impatrq/horus/horus_documentacion/Tabla costos.pdf

Componente | Cantidad | Precio Individual | Precio Parcial | Precio individual USD | Precio Parcial USD
Rasberry P9 4 Modelo B | 1 | $105.701,36 | $ 105.701,36 | $ 104,87 | $ 104,87
Raspberry Pi Pico | 2 | $12.279,000 | $ 24.558,00 | $ 12,17 | $ 24,33
Almacenamiento Externo Kingston | 1 | $12.698,00 | $ 12.698,00 | $ 12,58 | $ 12,58
Modulo Lora sx1278 | 2 | $17.487,00 | $ 34.974,00 | $ 17,35 | $ 34,70
Filamento Grilon3 PLA Gris | 3 | $14.987,00 | $ 44.961,00 | $ 14,87 | $ 44,61
Baterias de Gel 12v | 2 | $23.110,00 | $ 46.220,00 | $ 22,93 | $ 45,86
Camara Web Q Plus | 1 | $17.915,00 | $ 17.915,00 | $ 17,75 | $ 17,75
Módulo GPS | 1 | $12.638,00 | $ 12.638,00 | $ 12,54 | $ 12,54
Modulo A4988 (Drivers) | 2 | $2.079,00 | $ 4.158,00 | $ 2,06 | $ 4,12
PCB | 1 | $ 15.900,00 | $ 15.900,00 | $ 15,75 | $ 15,75
Plancha de aluminio 30x30 | 1 | $14.498,00 | $ 14.498,00 | $ 14,36 | $ 14,36
Cable dupont macho-hembra | 1 | $2.239,00 | $ 2.239,00 | $ 2,22 | $ 2,22
Cable dupont macho-macho | 1 | $2.229,00 | $ 2.229,00 | $ 2,21 | $ 2,21
Servo Digital Mg996 Mg996r | 2 | $12.100,00 | $ 24.200,00 | $ 12,00 | $ 24,00
Tira de Pines | 1 | $3.880,00 | $ 3.880,00 | $ 3,84 | $ 3,84
Servo Motor SG90 | 1 | $3.846,00 | $ 3.846,00 | $ 3,82 | $ 3,82
Total Pesos (Noviembre 2024): | $ 370.615,36 | Total USD: | $ 367,56
