impatrq/horus/Estructura_HORUS/peso_y_dimensiones.pdf

Pesos y tamaño
Estructura 400x400 peso 1kg motores 43x43x40 255g

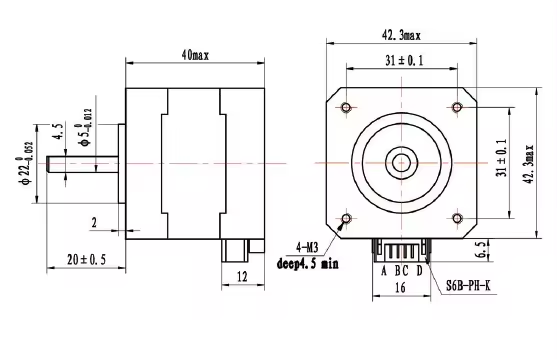
[picture p3: figure]

servo 40x20x44 peso 55g

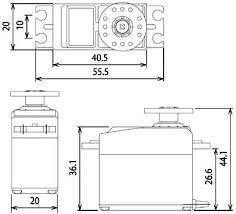
[picture p4: figure]

camara 36x36 peso 15g

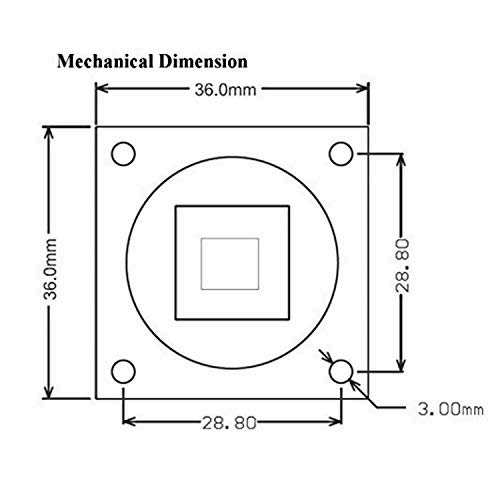
[picture p5: figure]

raspberry pi 4 88 x 58 x 18,5 peso 100g

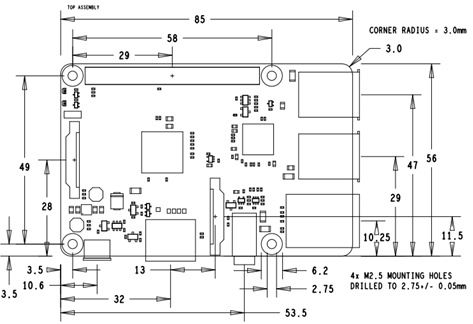
[picture p6: figure]

lectora de sd 45x21 peso 7.2g

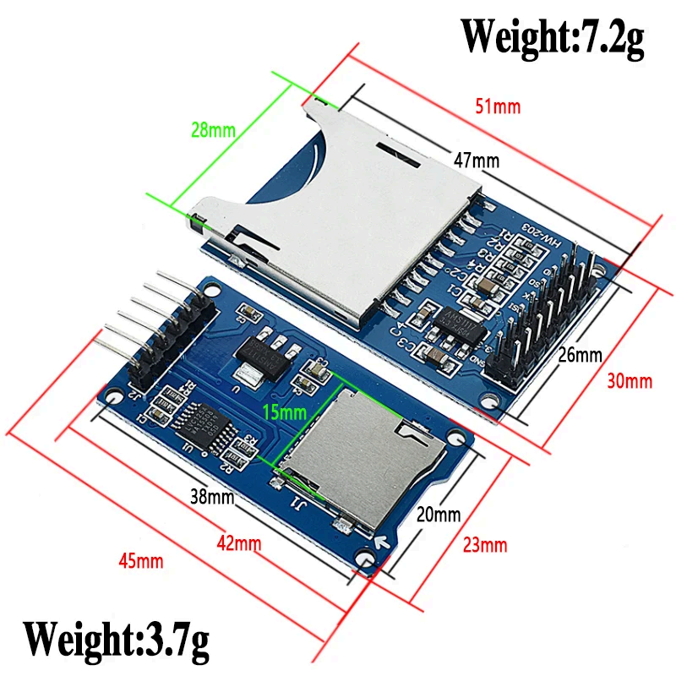
[picture p7: figure]

geolocalizador 35x25 peso 17g

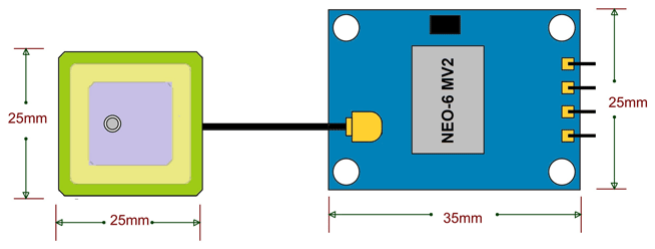
[picture p8: figure]

adaptador 16x15.2 peso 15g

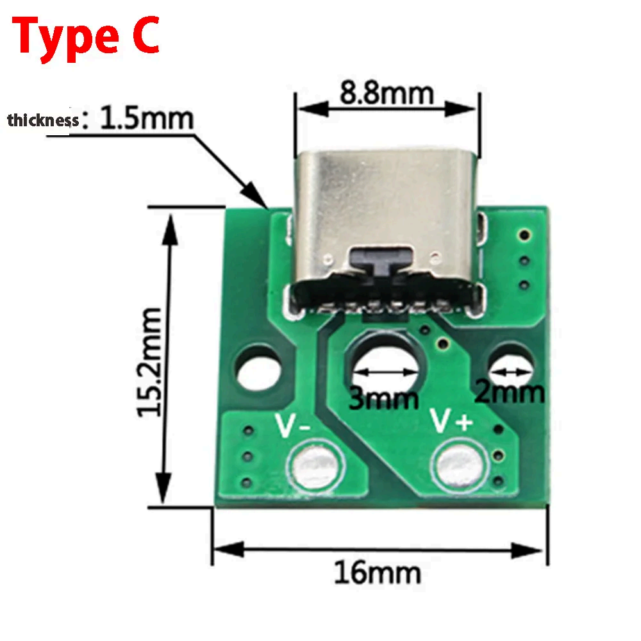
[picture p9: figure]

modulo rf 30x50 peso 20g

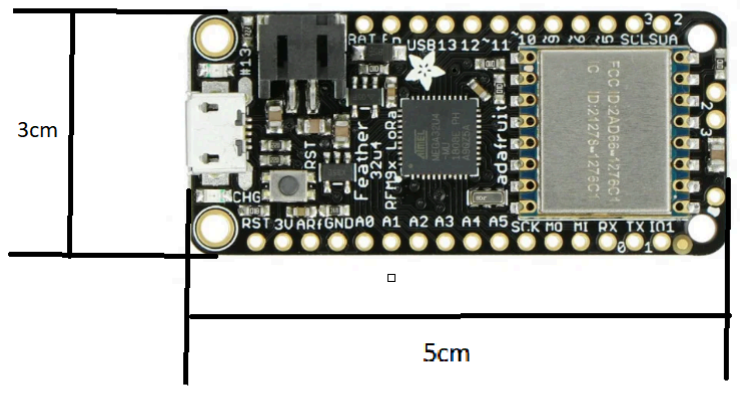
[picture p10: figure]

Bateria gel 12v 5ah 90x100x70

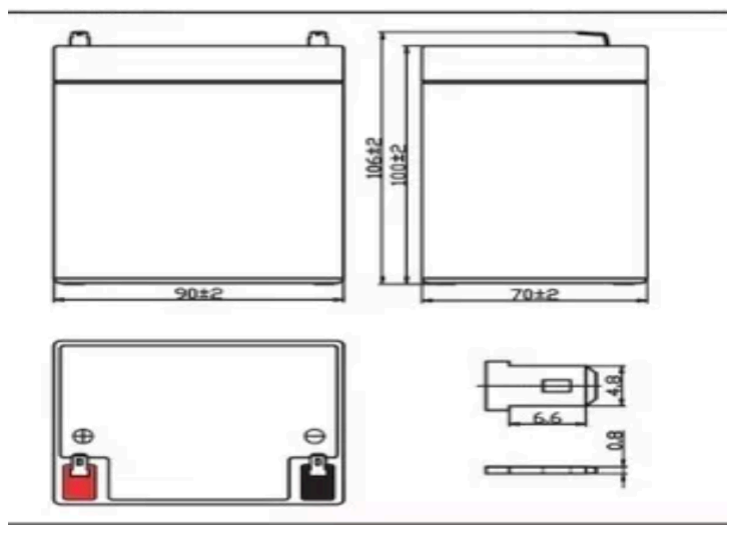
[picture p11: figure]
