impatrq/horus/Estructura_HORUS/Imagenes/adaptador eje elevador.png

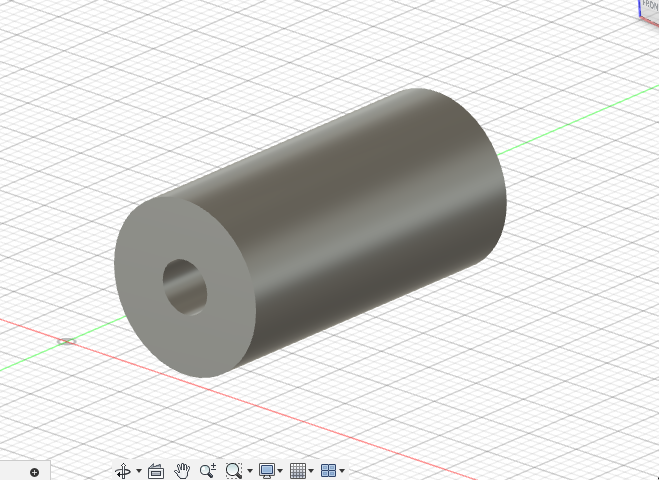
Estructura_HORUS/Imagenes/adaptador eje elevador.png
