impatrq/horus/Estructura_HORUS/Imagenes/agarre tuerca brazo elevador.png

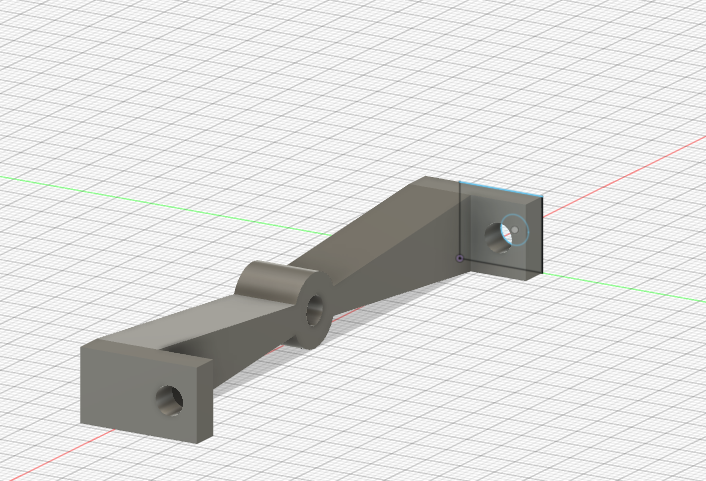
Estructura_HORUS/Imagenes/agarre tuerca brazo elevador.png
