impatrq/horus/Estructura_HORUS/Imagenes/base brazo.png

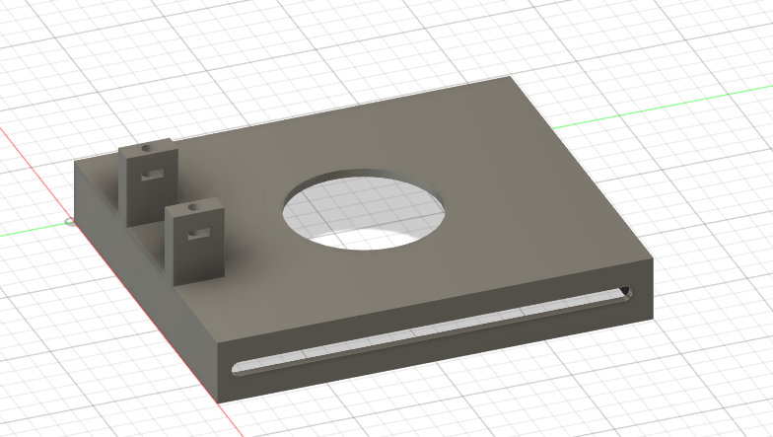
Estructura_HORUS/Imagenes/base brazo.png
