impatrq/horus/Estructura_HORUS/Imagenes/controladora sttepers.png

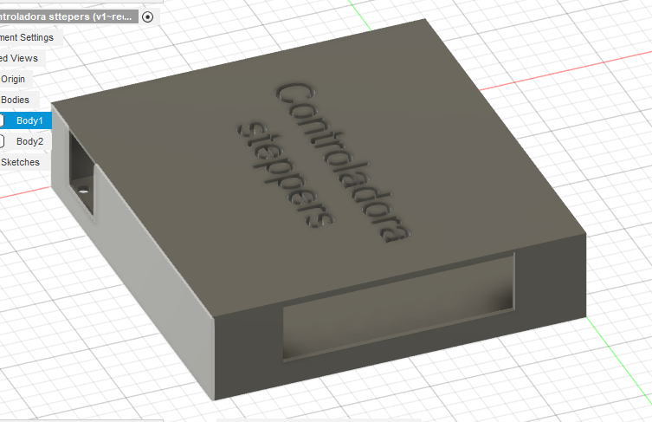
Estructura_HORUS/Imagenes/controladora sttepers.png
