impatrq/horus/Estructura_HORUS/Imagenes/refuerzo brazo.png

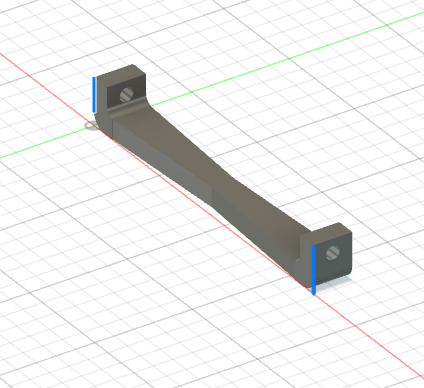
Estructura_HORUS/Imagenes/refuerzo brazo.png
