impatrq/horus/Estructura_HORUS/Imagenes/soporte bateria.png

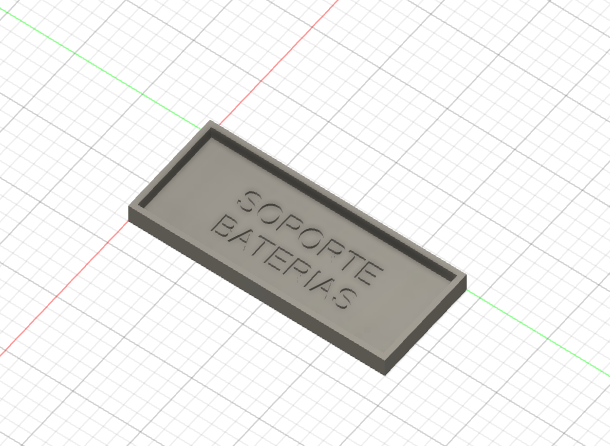
Estructura_HORUS/Imagenes/soporte bateria.png
