impatrq/horus/Estructura_HORUS/Imagenes/soporte camara.png

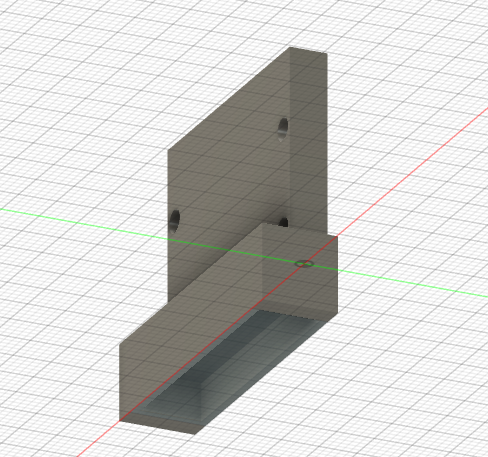
Estructura_HORUS/Imagenes/soporte camara.png
