impatrq/horus/Estructura_HORUS/Imagenes/soporte motor.png

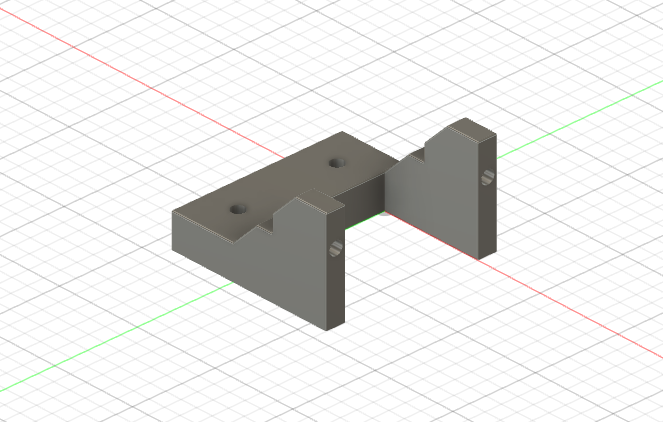
Estructura_HORUS/Imagenes/soporte motor.png
