impatrq/horus/Estructura_HORUS/Imagenes/suspension armada.png

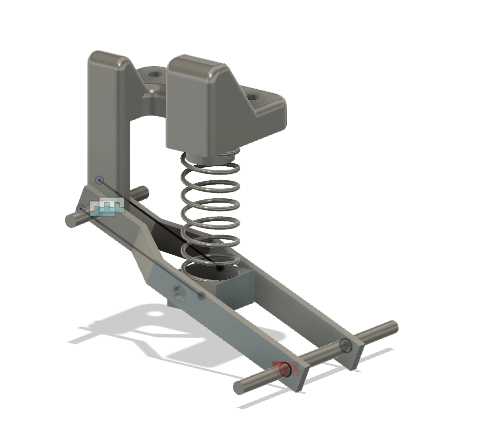
Estructura_HORUS/Imagenes/suspension armada.png
