impatrq/horus/Estructura_HORUS/Imagenes/tensor orugas.png

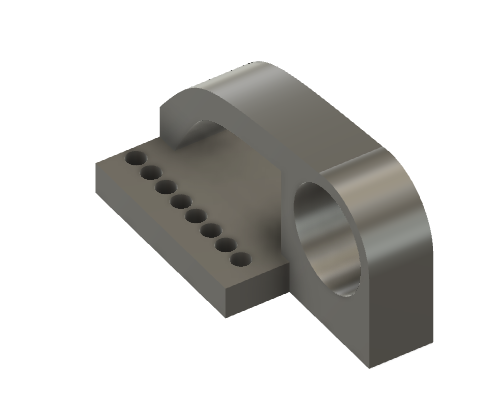
Estructura_HORUS/Imagenes/tensor orugas.png
