impatrq/horus/Estructura_HORUS/Primeros diseños/WhatsApp Image 2024-10-21 at 4.15.37 PM (1).jpeg

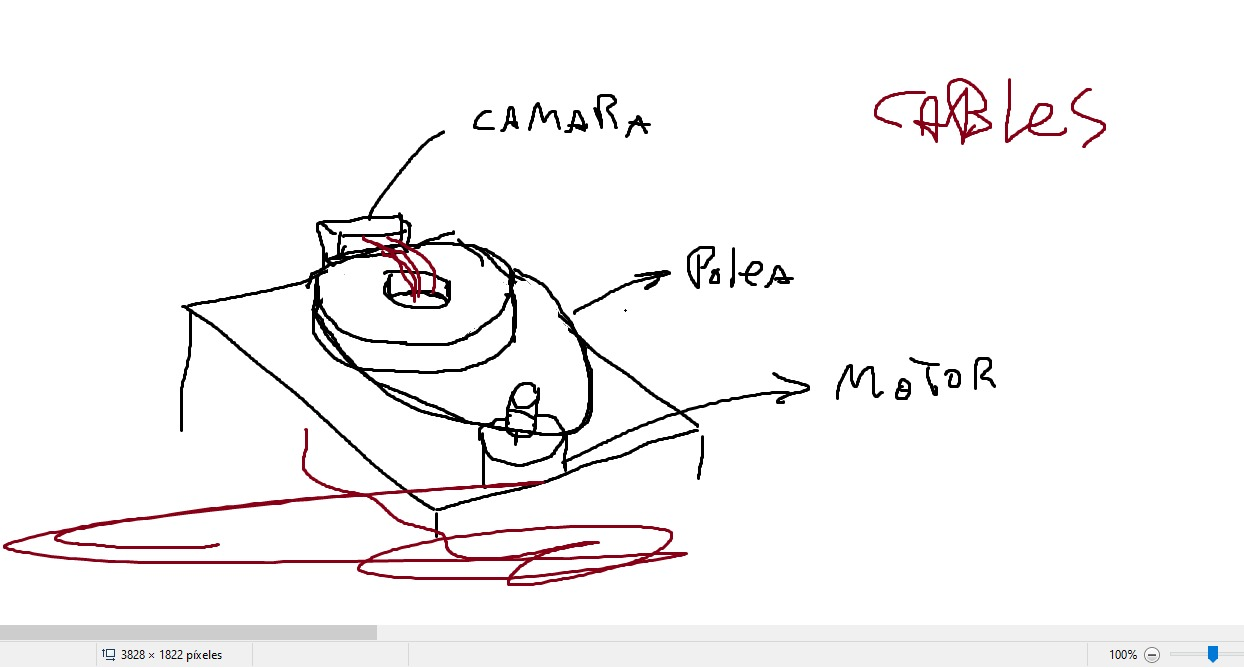
Estructura_HORUS/Primeros diseños/WhatsApp Image 2024-10-21 at 4.15.37 PM (1).jpeg
