impatrq/horus/horus_app/frontend/src/assets/boton-menos.png

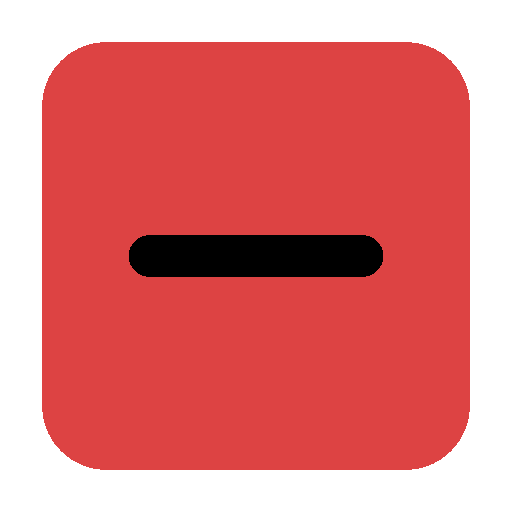
horus_app/frontend/src/assets/boton-menos.png
