impatrq/horus/horus_app/frontend/src/assets/delete.png

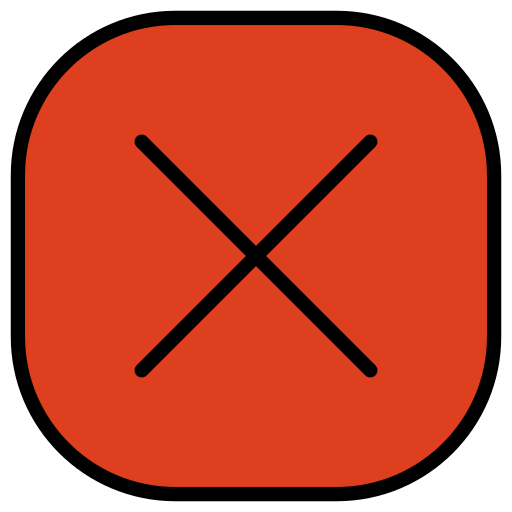
horus_app/frontend/src/assets/delete.png
