impatrq/horus/horus_app/frontend/src/assets/error.png

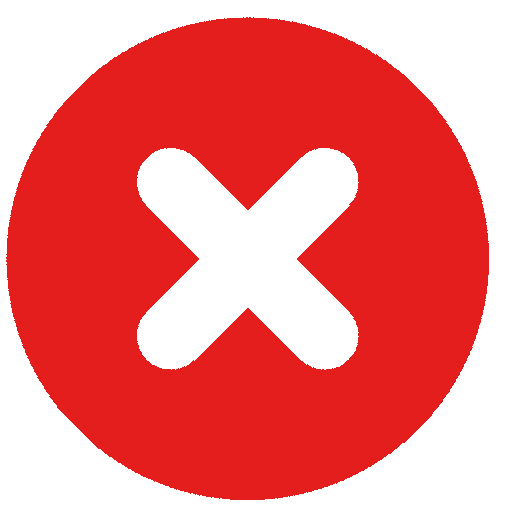
horus_app/frontend/src/assets/error.png
