impatrq/horus/horus_app/frontend/src/assets/mapas-y-banderas (1).png

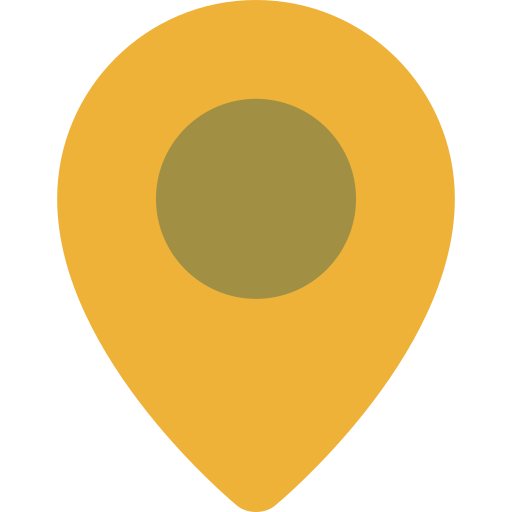
horus_app/frontend/src/assets/mapas-y-banderas (1).png
