impatrq/horus/horus_app/frontend/src/assets/mapas-y-banderas (2).png

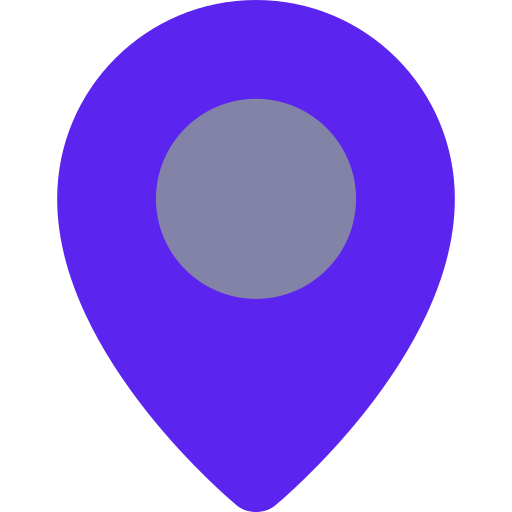
horus_app/frontend/src/assets/mapas-y-banderas (2).png
