impatrq/horus/horus_app/frontend/src/assets/Ojo de Horus.png

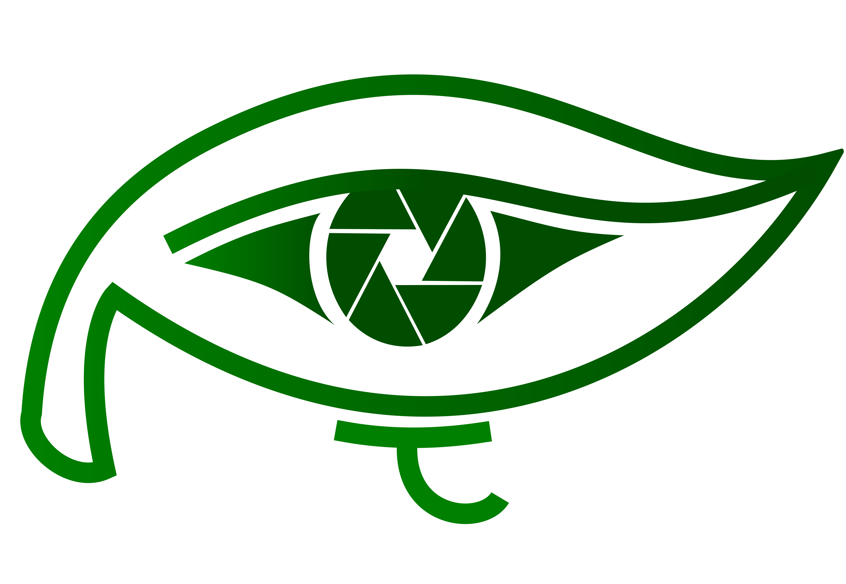
horus_app/frontend/src/assets/Ojo de Horus.png
