impatrq/horus/horus_documentacion/HORUS.jpg.jpeg

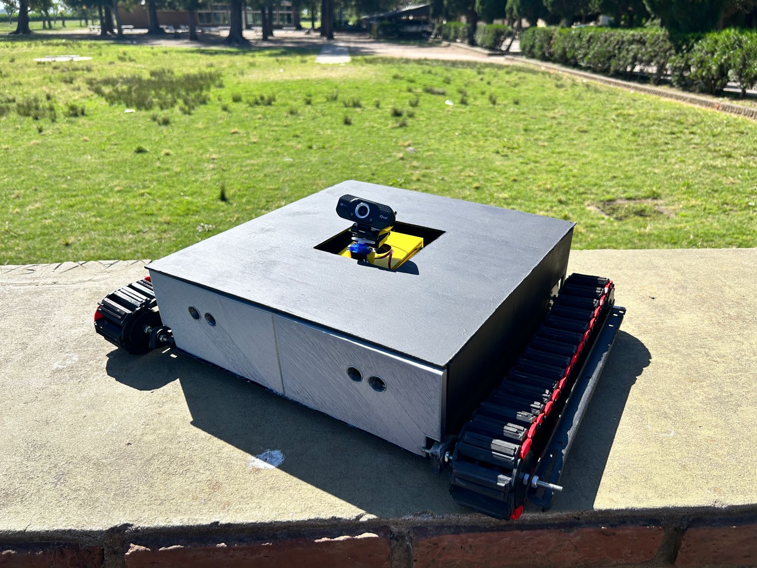
horus_documentacion/HORUS.jpg.jpeg
