impatrq/horus/horus_documentacion/Minimum valiable product.png

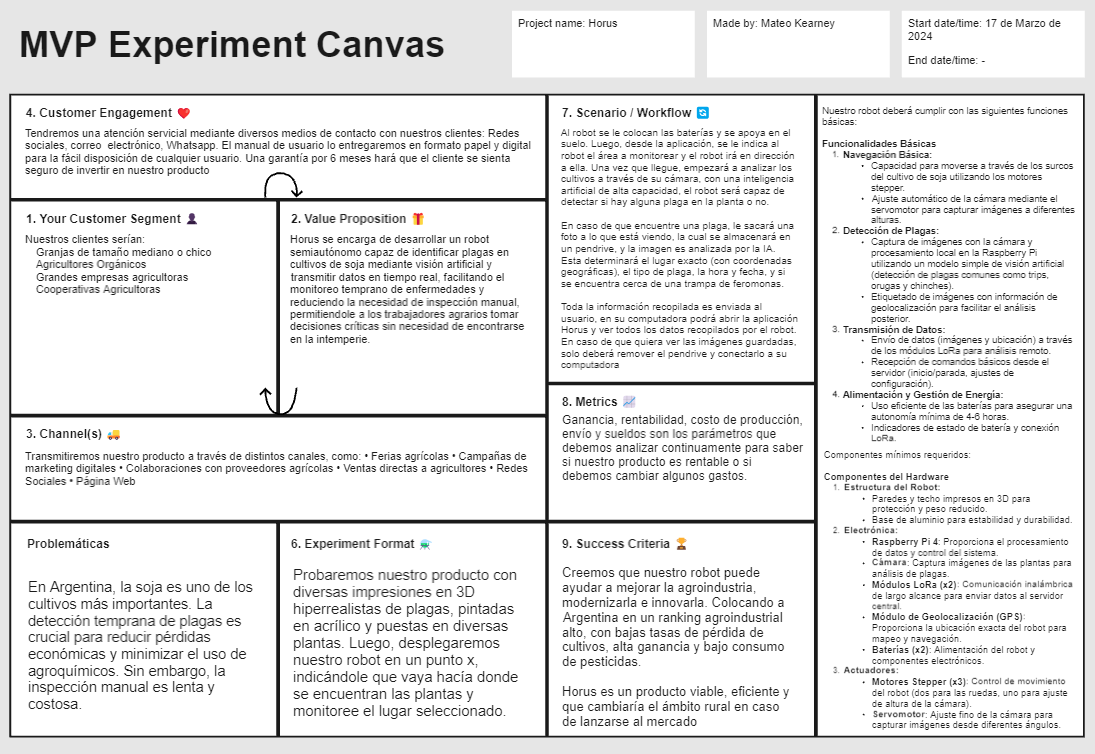
horus_documentacion/Minimum valiable product.png
