impatrq/horus/horus_electronics/Archivos Kicad pcb/NewEra.png

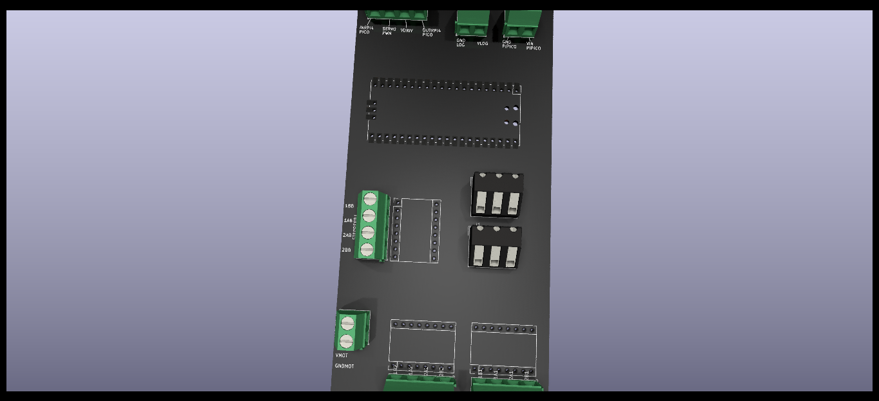
horus_electronics/Archivos Kicad pcb/NewEra.png
