impatrq/horus/horus_electronics/Archivos Kicad pcb/PCB STEPPER BRAZO/Screenshot_3.png

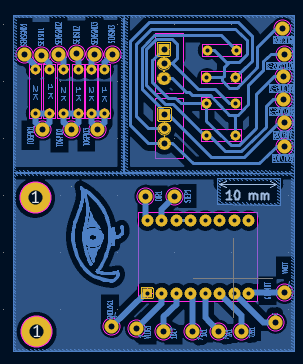
horus_electronics/Archivos Kicad pcb/PCB STEPPER BRAZO/Screenshot_3.png
