impatrq/horus/horus_electronics/misc Imagenes/3.png

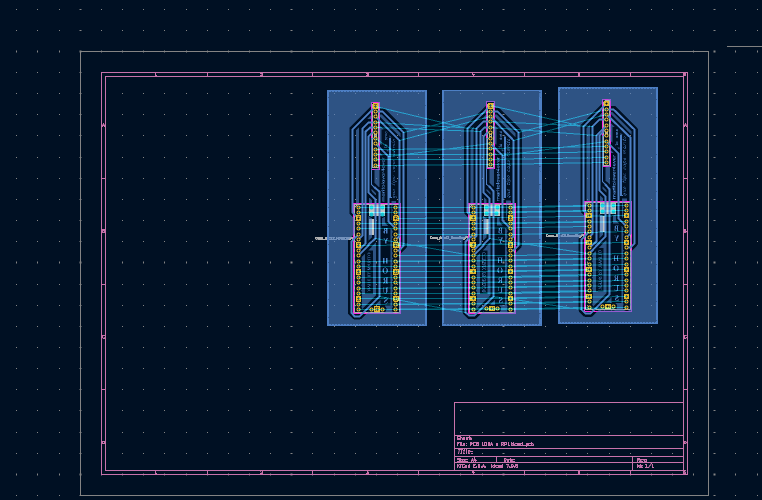
horus_electronics/misc Imagenes/3.png
