impatrq/horus/horus_electronics/misc Imagenes/A4988 conection diagram.png

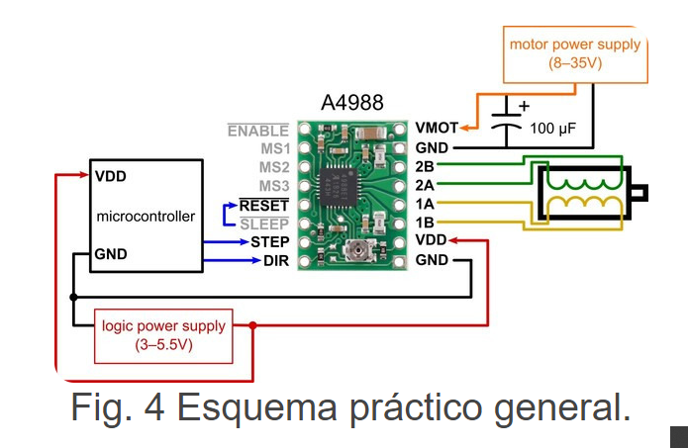
horus_electronics/misc Imagenes/A4988 conection diagram.png
