impatrq/horus/horus_electronics/misc Imagenes/NewEraVISUAL.png

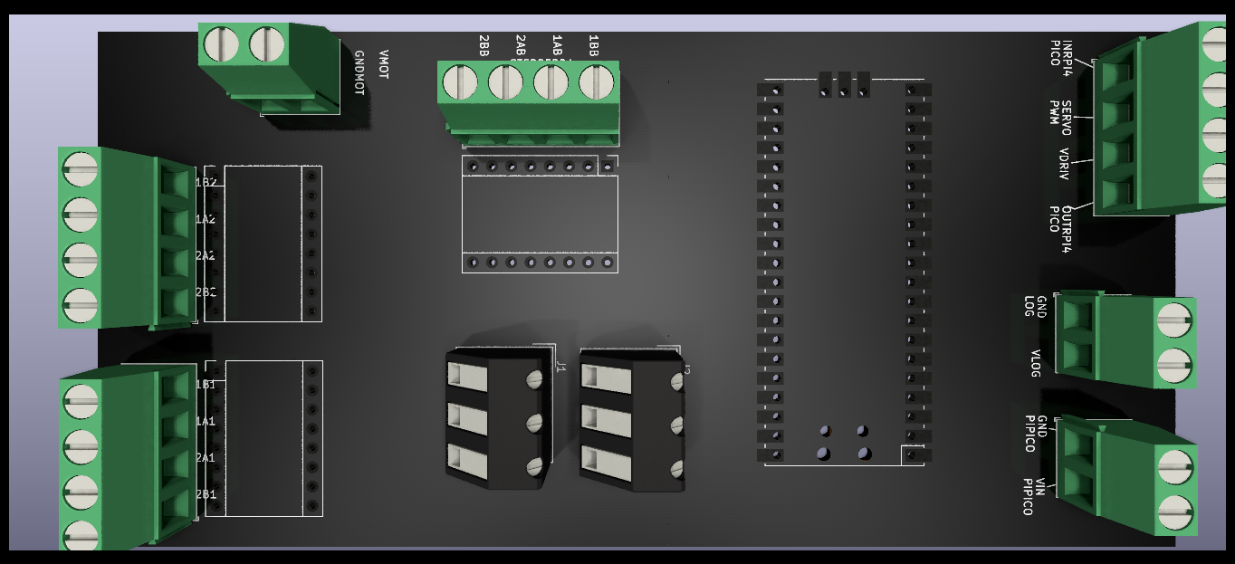
horus_electronics/misc Imagenes/NewEraVISUAL.png
