impatrq/horus/horus_electronics/misc Imagenes/pangeaPuenteh.jpg

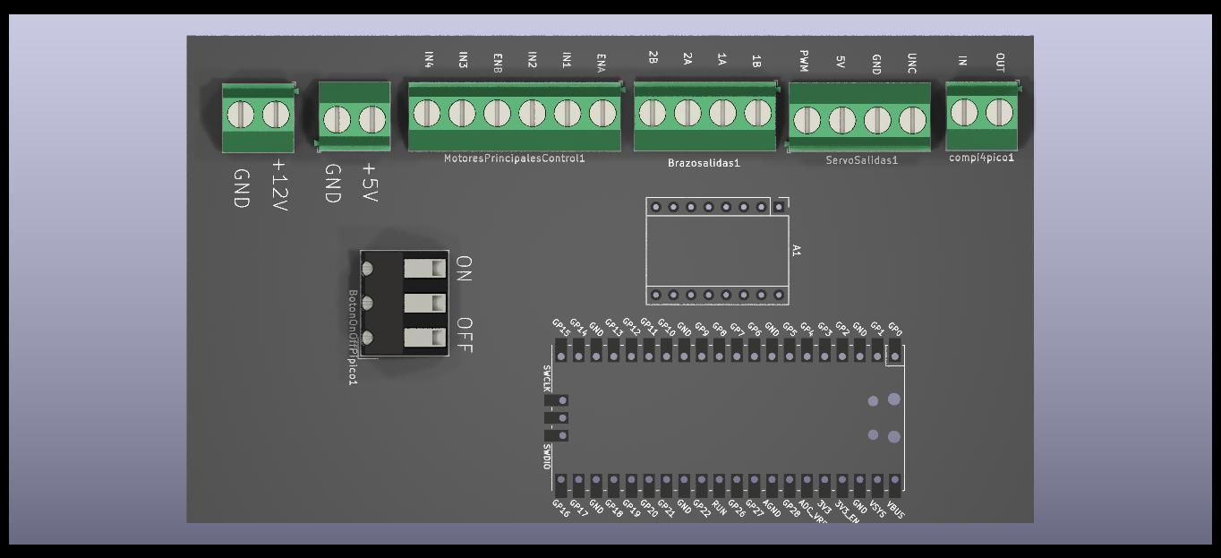
horus_electronics/misc Imagenes/pangeaPuenteh.jpg
