impatrq/horus/horus_electronics/misc Imagenes/pangeaPuenteh.jpg.png

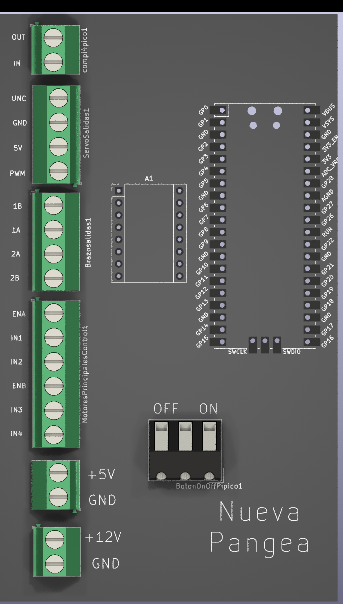
horus_electronics/misc Imagenes/pangeaPuenteh.jpg.png
