impatrq/horus/horus_electronics/misc Imagenes/Screenshot_1.png

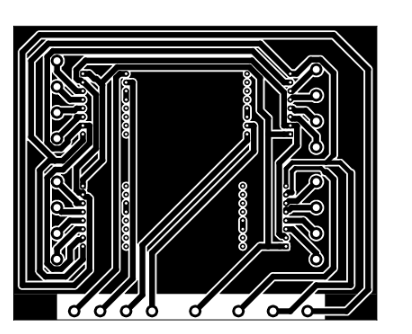
horus_electronics/misc Imagenes/Screenshot_1.png
