impatrq/horus/horus_electronics/misc Imagenes/Screenshot_3.png

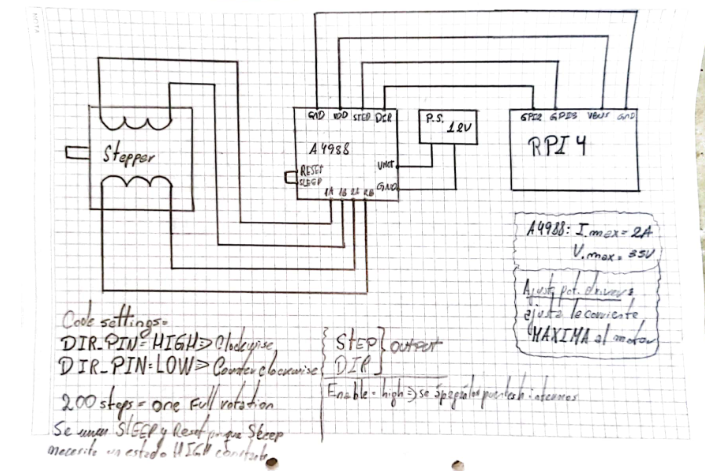
horus_electronics/misc Imagenes/Screenshot_3.png
