impatrq/horus/horus_electronics/misc Imagenes/Screenshot_4.png

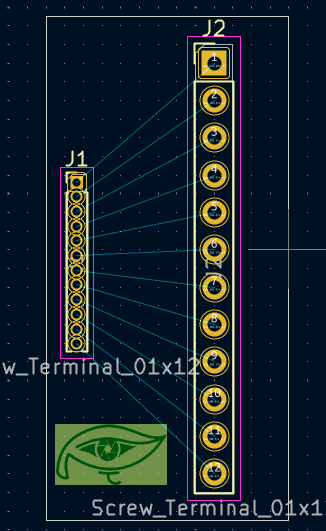
horus_electronics/misc Imagenes/Screenshot_4.png
