impatrq/horus/horus_electronics/misc Imagenes/Screenshot_5.png

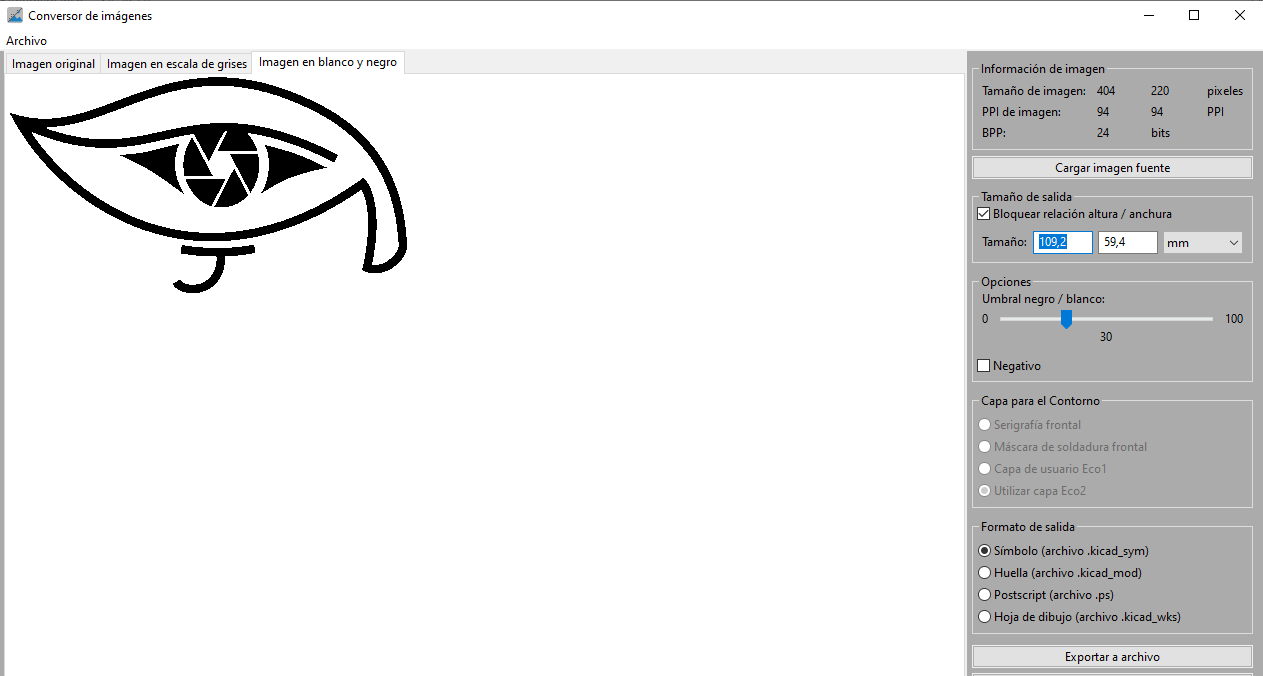
horus_electronics/misc Imagenes/Screenshot_5.png
