impatrq/horus/horus_electronics/misc Imagenes/Screenshot_6.png

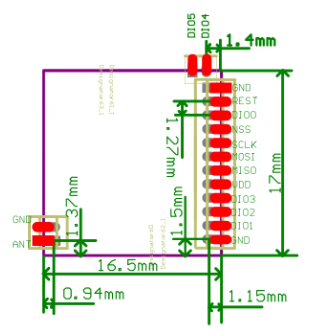
horus_electronics/misc Imagenes/Screenshot_6.png
