impatrq/horus/horus_paginaWeb/paginaWeb/dist/assets/Github-nDIyJ6BR.png

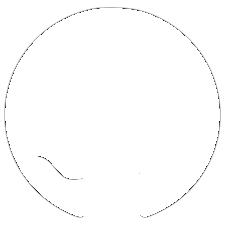
horus_paginaWeb/paginaWeb/dist/assets/Github-nDIyJ6BR.png
