impatrq/horus/horus_paginaWeb/paginaWeb/dist/assets/LinkedinBlanco-4YxeiaYb.png

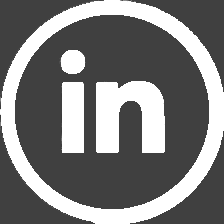
horus_paginaWeb/paginaWeb/dist/assets/LinkedinBlanco-4YxeiaYb.png
