impatrq/horus/horus_paginaWeb/paginaWeb/dist/assets/marito-BGvwKk_j.jpg

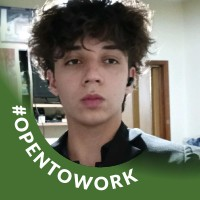
horus_paginaWeb/paginaWeb/dist/assets/marito-BGvwKk_j.jpg
