impatrq/horus/Estructura_HORUS/Archivos STL/estrcutura principal susp 1.stl

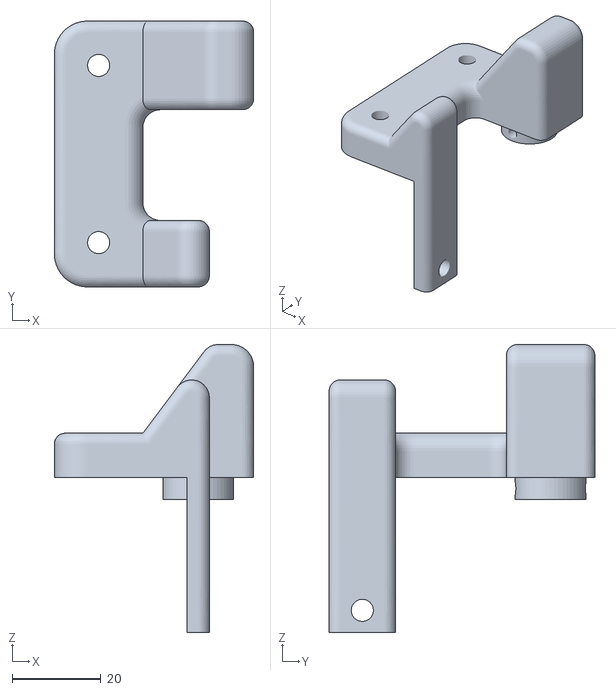
[picture p89: CAD file, 2024-11-26]
Estructura_HORUS/Archivos STL/estrcutura principal susp 1.stl
45.0 x 60.0 x 65.0
