impatrq/horus/Estructura_HORUS/Archivos STL/soporte baterias.stl

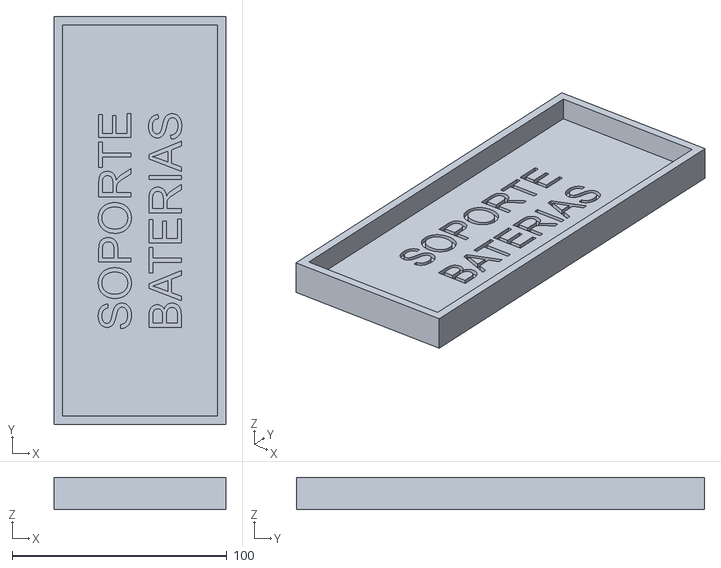
[picture p90: CAD file, 2024-11-26]
Estructura_HORUS/Archivos STL/soporte baterias.stl
80.0 x 190.0 x 15.0
