impatrq/horus/Estructura_HORUS/Archivos STL/soport servoo.stl

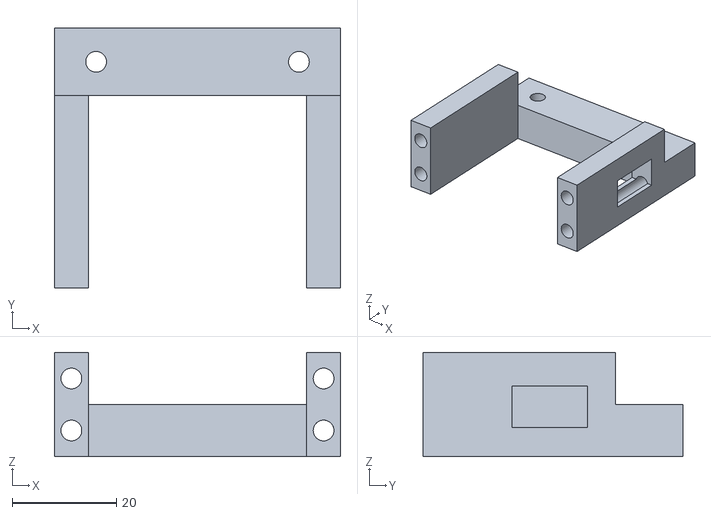
[picture p91: CAD file, 2024-11-26]
Estructura_HORUS/Archivos STL/soport servoo.stl
55.0 x 50.0 x 20.0
