impatrq/horus/Estructura_HORUS/Archivos STL/soporte motores.stl

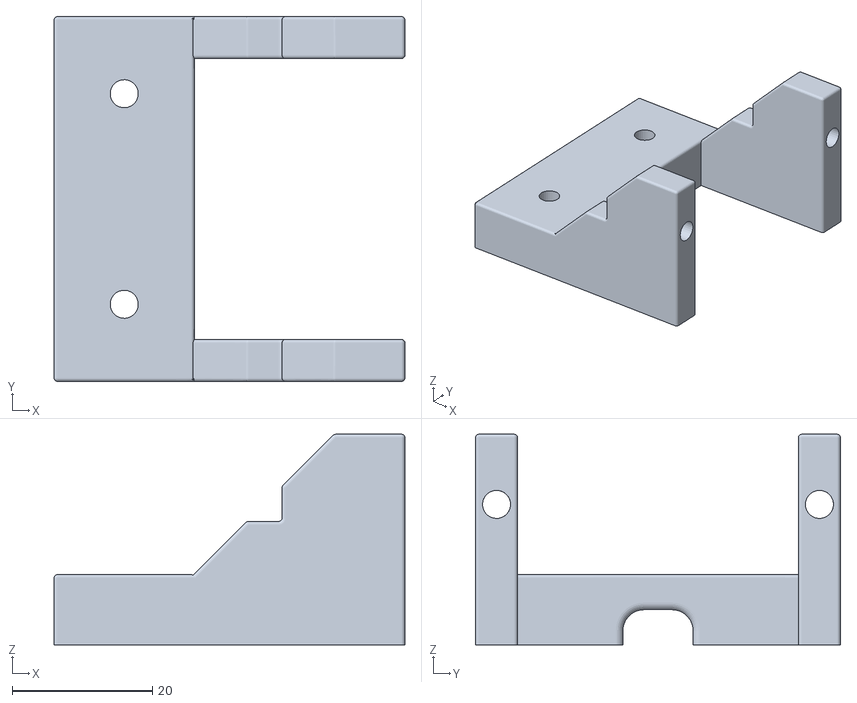
[picture p92: CAD file, 2024-11-26]
Estructura_HORUS/Archivos STL/soporte motores.stl
50.0 x 52.0 x 30.0
