impatrq/horus/Estructura_HORUS/Archivos STL/refuerzo brazo elevador.stl

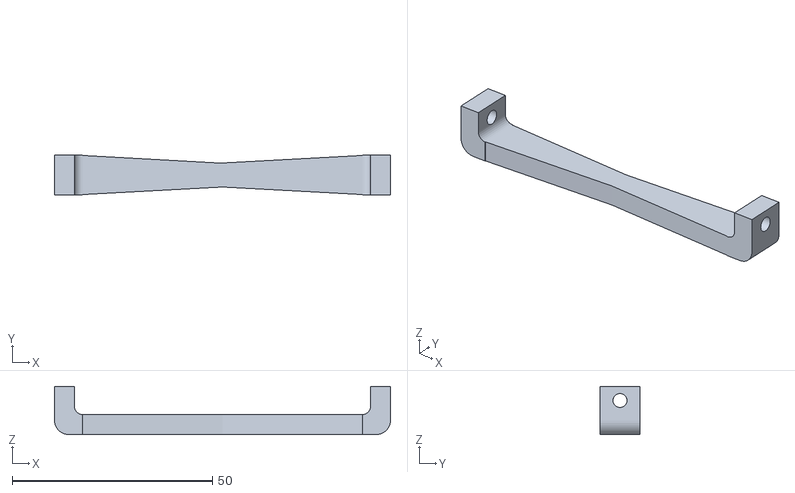
[picture p93: CAD file, 2024-11-26]
Estructura_HORUS/Archivos STL/refuerzo brazo elevador.stl
84.0 x 10.0 x 12.0
