impatrq/horus/Estructura_HORUS/Archivos STL/pasador orugas.stl

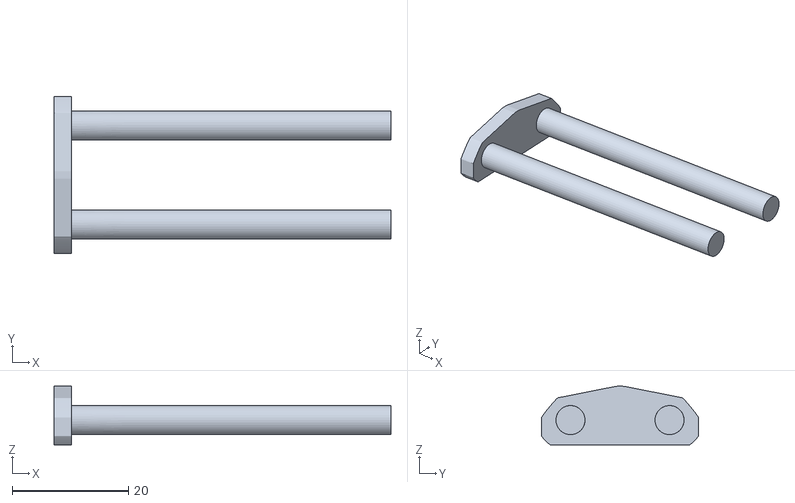
[picture p94: CAD file, 2024-11-26]
Estructura_HORUS/Archivos STL/pasador orugas.stl
58.0 x 27.0 x 10.1
