impatrq/horus/Estructura_HORUS/Archivos STL/tensor orgas .stl

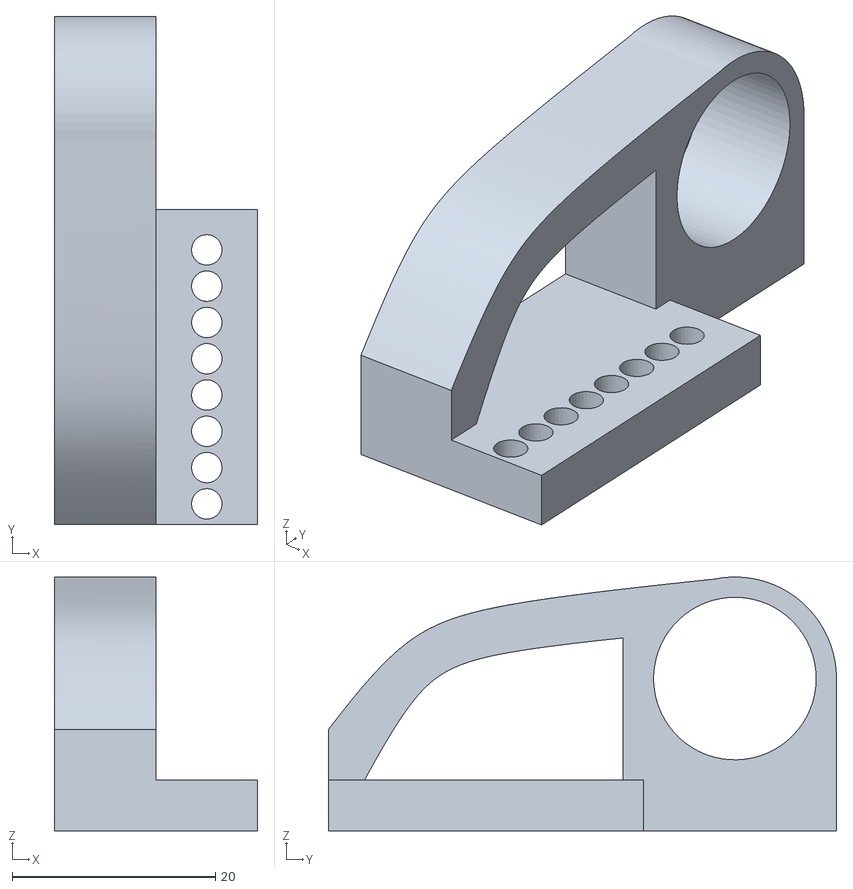
[picture p95: CAD file, 2024-11-26]
Estructura_HORUS/Archivos STL/tensor orgas .stl
20.0 x 50.0 x 25.0
