impatrq/horus/Estructura_HORUS/Archivos STL/rueda suspension .stl

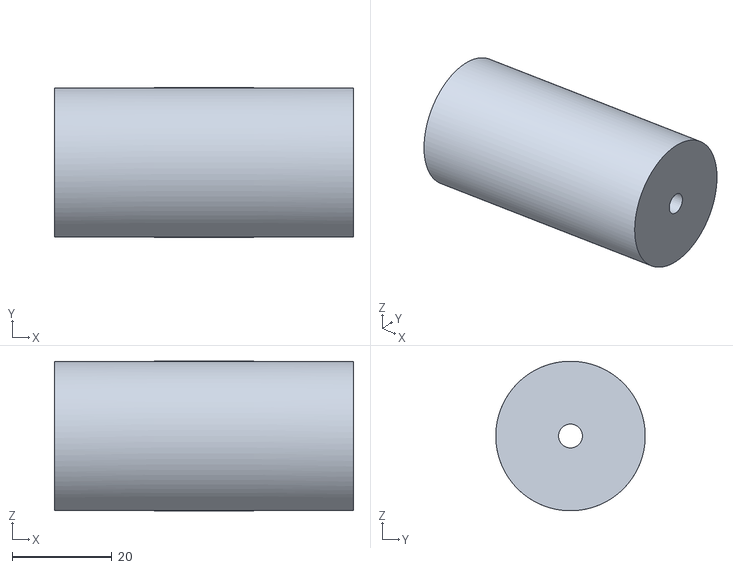
[picture p96: CAD file, 2024-11-26]
Estructura_HORUS/Archivos STL/rueda suspension .stl
60.0 x 30.0 x 30.0
