impatrq/horus/Estructura_HORUS/Archivos STL/soporte cam.stl

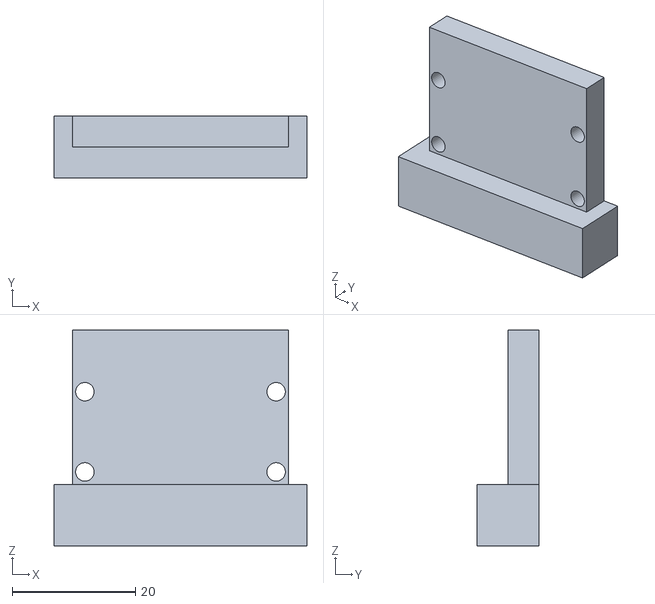
[picture p97: CAD file, 2024-11-26]
Estructura_HORUS/Archivos STL/soporte cam.stl
41.0 x 10.0 x 35.0
