impatrq/horus/Estructura_HORUS/Archivos STL/trabitas orugas.stl

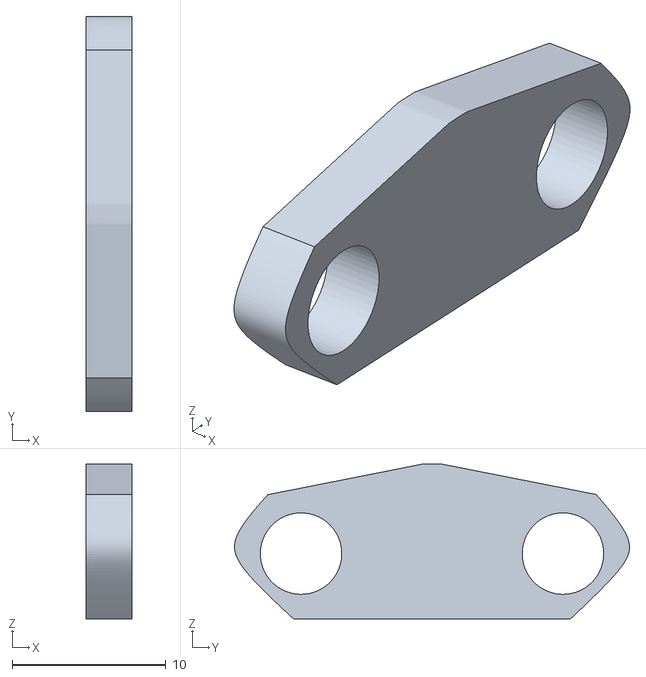
[picture p98: CAD file, 2024-11-26]
Estructura_HORUS/Archivos STL/trabitas orugas.stl
3.00 x 25.7 x 10.1
