impatrq/horus/Estructura_HORUS/Archivos STL/tapa controladora sttepers.stl

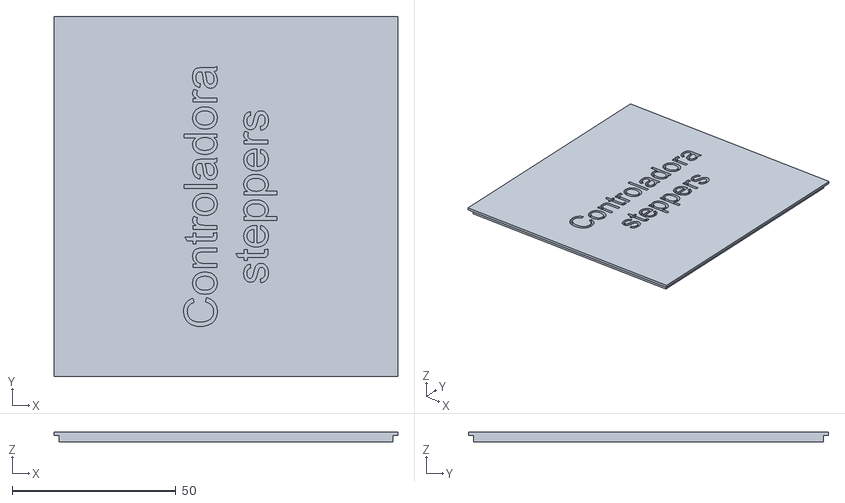
[picture p99: CAD file, 2024-11-26]
Estructura_HORUS/Archivos STL/tapa controladora sttepers.stl
105.0 x 110.0 x 3.00
