impatrq/horus/Estructura_HORUS/Archivos STL/agarre resorte.stl

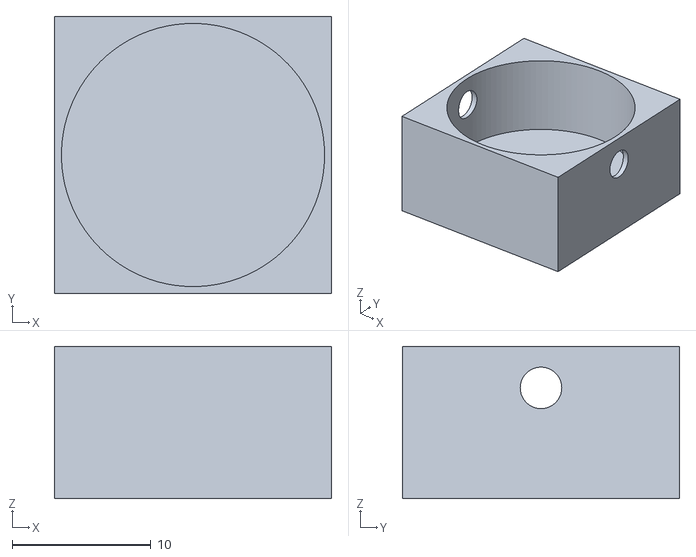
[picture p100: CAD file, 2024-11-26]
Estructura_HORUS/Archivos STL/agarre resorte.stl
20.0 x 20.0 x 11.0
