impatrq/horus/Estructura_HORUS/Archivos STL/base brazo elevador.stl

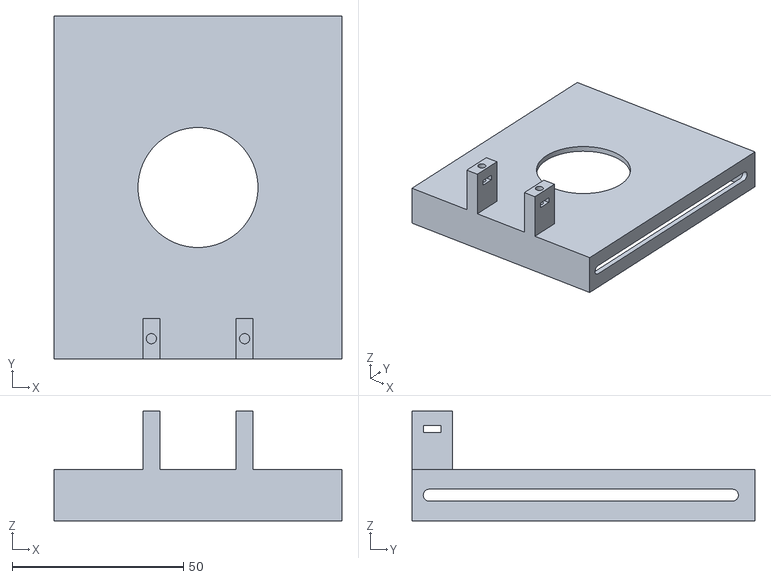
[picture p101: CAD file, 2024-11-26]
Estructura_HORUS/Archivos STL/base brazo elevador.stl
84.0 x 100.0 x 32.0
