impatrq/horus/Estructura_HORUS/Imagenes/brazo armado.png

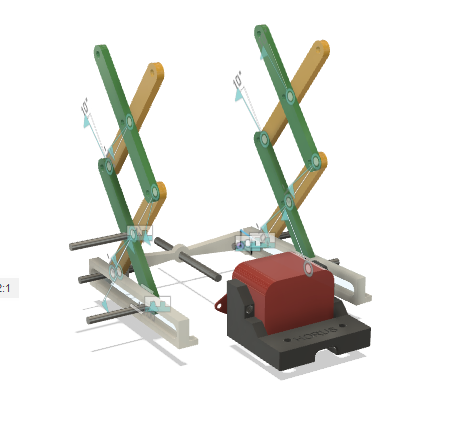
Estructura_HORUS/Imagenes/brazo armado.png
