impatrq/horus/horus_electronics/PDFS IMPRIMIBLES/PCB LORA TO RPI PICO.pdf

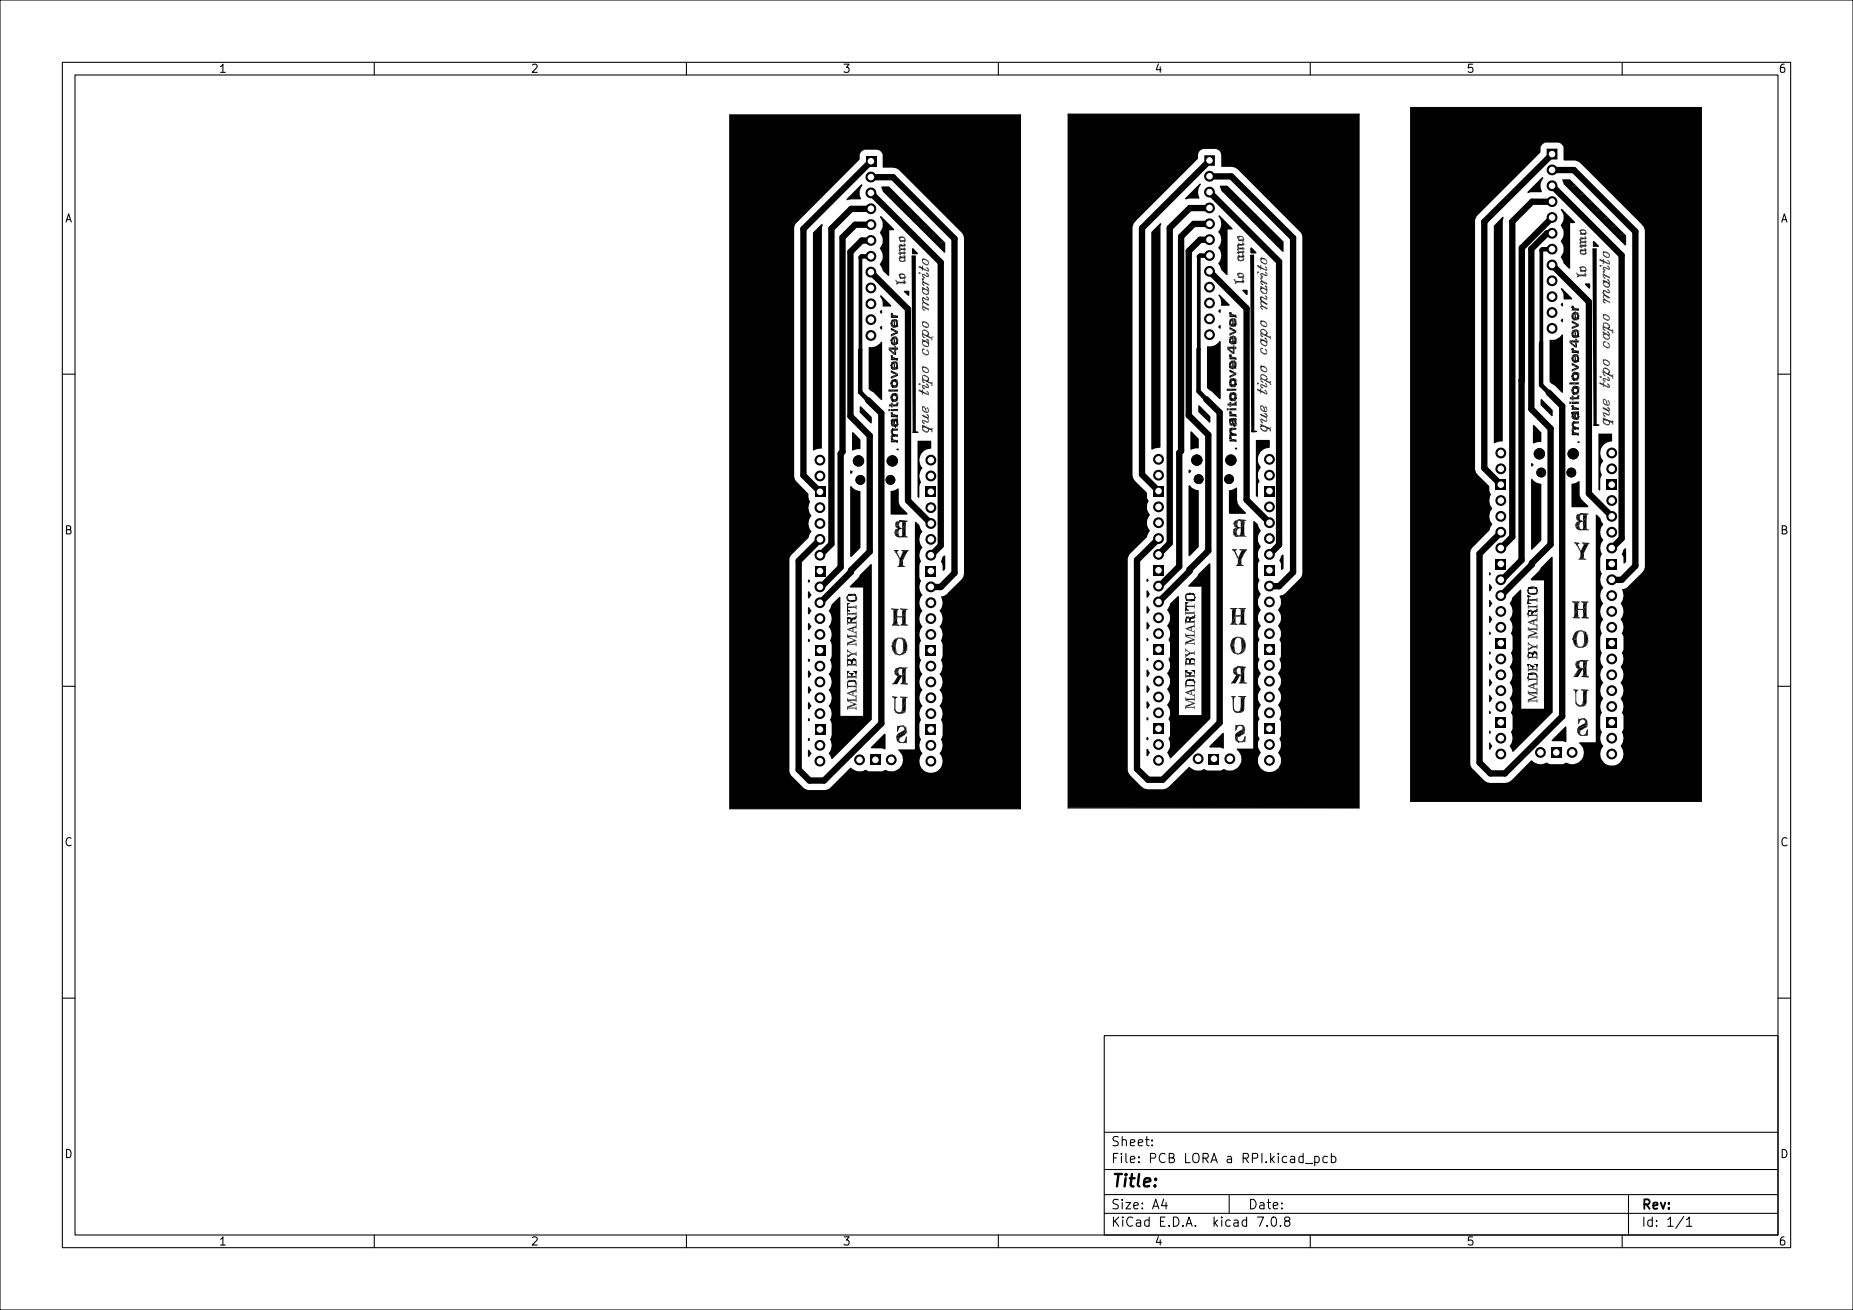
[picture p120: page 1]
