impatrq/horus/horus_documentacion/Medalla - Feed de Instagram.pdf

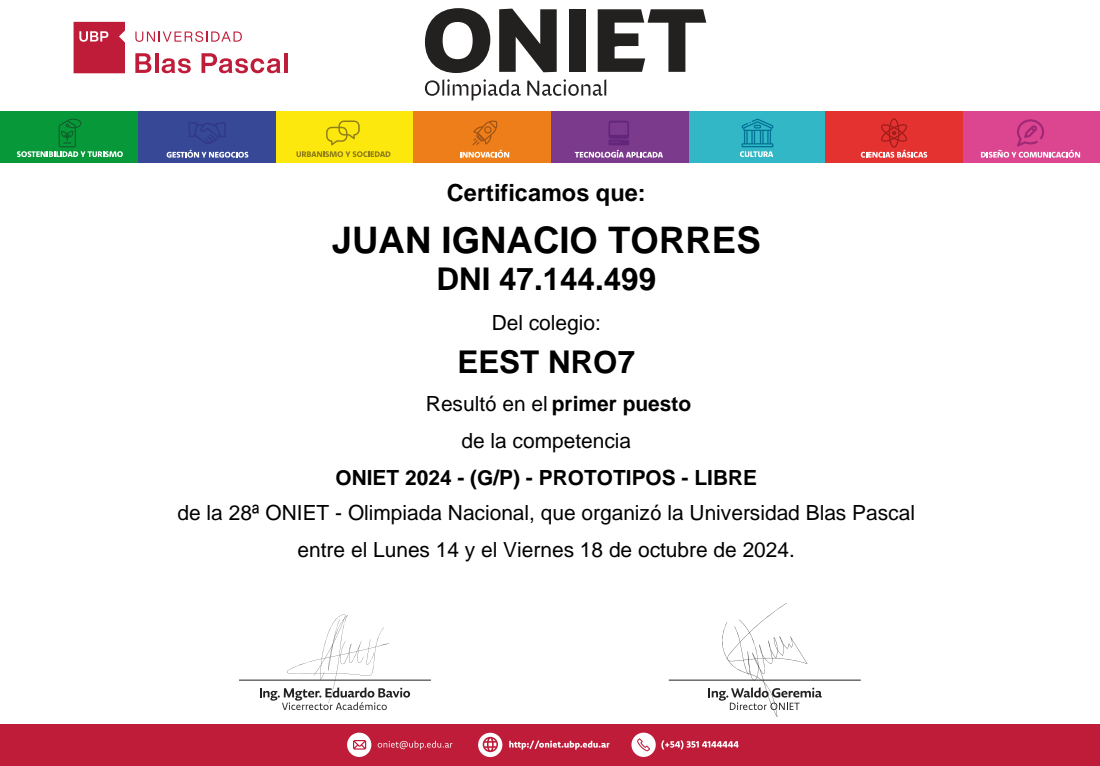
[picture p121: page 1]
Del colegio: EEST NRO7

Certificamos que:
JUAN IGNACIO TORRES
DNI 47.144.499

Resultó en el primer puesto
de la competencia

ONIET 2024 - (G/P) - PROTOTIPOS - LIBRE

de la 28ª ONIET - Olimpiada Nacional, que organizó la Universidad Blas Pascal

entre el Lunes 14 y el Viernes 18 de octubre de 2024.
