impatrq/horus/horus_electronics/Codigos/stepper.py

from machine import Pin, Timer
import utime
 
dir_pin = Pin(16, Pin.OUT)
step_pin = Pin(17, Pin.OUT)
steps_per_revolution = 200
led = Pin(25, Pin.OUT)

led.on()
# Initialize timer
tim = Timer()
 
def step(t):
    global step_pin
    step_pin.value(not step_pin.value())
 
def rotate_motor(delay):
    # Set up timer for stepping
    tim.init(freq=1000000//delay, mode=Timer.PERIODIC, callback=step)
 
def loop():
    while True:
        # Set motor direction clockwise
        dir_pin.value(1)
 
        # Spin motor slowly
        rotate_motor(2000)
        utime.sleep_ms(steps_per_revolution)
        tim.deinit()  # stop the timer
        utime.sleep(1)
        print("rotato")
        # Set motor direction counterclockwise
        dir_pin.value(0)
 
        # Spin motor quickly
        rotate_motor(1000)
        utime.sleep_ms(steps_per_revolution)
        tim.deinit()  # stop the timer
        utime.sleep(1)
 
if __name__ == '__main__':
    loop()
